coy-coburn/Team24/Old Project/Modified White Paper.pptx

Smart Sprinkler System Project Goal: The goal of this project is to create a system where a person’s lawn is routinely probed and cared for by an automatic sprinkler system. Deliverables Fall 2015: Robot w/ probe, weather monitoring via internet, w/ interface app Spring 2016: Robot charging station, Robot collision-avoiding sensors, pathing memory within box, controller connected to sprinkler system

Team 24: Coy Coburn, Daniel Miller, Michael Turner, Tyler Castro

Robot maneuvering

Power

Controller

Mobile app

Robot sensors

Moisture measurement

Weather data mining

## Slide 2

Subsystem | Primarily Responsible Team Member | Student Responsibilities/ Tasks
Power | Daniel | Prepare the necessary power supply for both the probe as well as the sprinkler system.
Controller | Coy | Create a connection between the master controller with its slave connections; these include the probe, the sprinkler system, and the interface app.
Robot maneuvering | Daniel | Enhance the robot’s ability to maneuver off-terrain and possess the ability to set a route for probing locations.
Robot sensoring | Michael | The robot will need the functions to sense its surroundings and take necessary precautions to avoid obstacles and safely maneuver a lawn.
Moisture measurement | Tyler | IR sensors will be set to sample water moisture in multiple locations in the lawn and reset said probe.
Mobile App | Coy | A mobile app will be created for a user to view sprinkler settings as well as make changes to planned watering for the week or its default.
Weather Data Mining | Michael | The sprinkler master controller will need to connect to weather websites via internet so to plan watering settings for the upcoming week.

## Slide 3

INTERNET

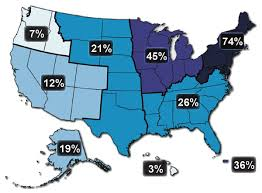
[picture p73: figure]

PRECIPITATION DATA

Control Box
Will handle all the data analysis and communication. Will also charge the robot.

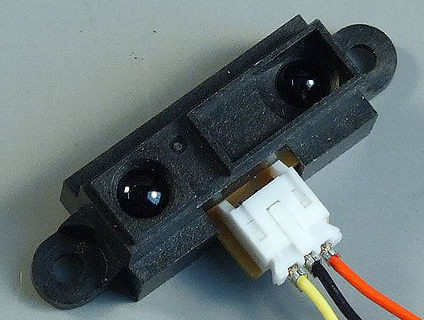
[picture p74: figure]

IR DATA

DATA RESULTS

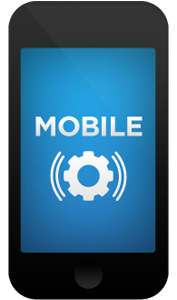
[picture p75: figure]
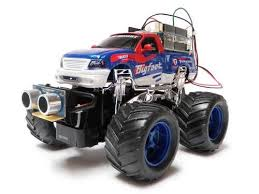
[picture p76: figure]

LOCATION DATA

POWER

USER FEEDBACK

## POWER

- Functional requirements-Provide power for the control station, provide charging capability for the robot
- Design parameters- Central control must be able to provide correct power requirements for the main controller and robot charge station.
- Primary constraints- Step down from 120V AC to microcontroller voltage and battery charging voltage
- Limiting factors-cost, size, Portability

## POWER

| Cost of power (Least important) | Size | Portability (most important)
Battery | High,frequent changing of batteries | Medium, depends on battery type | High
Wall outlet | Low | Medium | Low, needs cord
Custom (outlet/battery combination) | Medium | Medium, depends on battery type | Medium, outlet for controller but batteries for robot

## POWER

We selected the combination of batteries for the robot and direct connection to a wall outlet for the station housing a charging station and the microcontroller for the entire system. The station would consume too much power to rely on batteries, and the cost would become too high. In order to keep the robot mobile, we have decided to give it batteries while allowing it to charge while not in use in the station.

## CONTROLLER

- Functional requirements-can send and receive data from the robot and the mobile device. Will also analyze data taken from the robot and the internet. Control the sprinklers
- Design parameters-it will need reliable wifi connection with internet and robot. The system will need adequate memory to store and calculate data. GPIO pins are needed for sensor connections.
- Primary constraints- TCP function is preferred, a RAM of at least 256 mB and max of 1kB flash is needed. At least 10 pins will be needed
- Limiting factors-cost, processing time, memory size, Wi-Fi/bluetooth, external interfacing options, and ease of programing

## CONTROLLER

| cost (most Important) | processing time | memory size | Wi-Fi (least Important) | external interfacing options
Raspberry Pi B+ | $29.95 | 700 MHz (SoC) | 512 mB (RAM) | Ethernet port, can use wifi adapter | 26 GPIO
RCM5400W | $119 | 74 MHz (microprocessor) | 512 mB (RAM) | Integrated | 39 GPIO, startup,status, reset in/out
BeagleBone Black | $55 | 1 GHz (SoC) | 512 mB (SDRAM) | Ethernet port, can use wifi adapter | 46 GPIO
TI Tiva | $20 | 140 MHz | 256 mB (SRAM) | Ethernet port, can use wifi adapter | 40 GPIO

## CONTROLLER

While most, if not all, of the choices would probably work for our controller, the TI Tiva board was chosen for its relatively cheap price and met all of the required constraints. While the Raspberyy Pi B+ and Beaglebone Black were also decent choices, the are System on Chips, which is much more than we actually need.

## ROBOT MANEUVERING

- Functional requirements-navigate multiple terrains and location knowledge. It will also need wifi capability with the controller.
- Design parameters- the motors must not deplete the battery before it has completed its circuit. Motors must also possess enough torque to move the robot.
- Primary constraints- less than 10 A on battery draw, enough torque to easily move at most 2.5 kg load.
- Limiting factors- torque, power usage, and cost

## ROBOT MANEUVERING

| Torque (kg-cm) (40%) | Power usage (30%) | Cost (30%)
HS-422 Servo Motor | 4.1 | .9 (No-load) at 6.0 V | $9.69 * 2
DC Toy / Hobby Motor | .02 | .42 W (No-load) 1.5 W (loaded) at 6.0 V | $1.95 * 2
2WD microcontoller platform | 1.92 | .426 W (No load) 2.82 W (loaded at 6.0 V | $22.49
B0081C5B80 | .08 | 1.5 W (loaded) at 6.0 V | $6.40 * 2

## ROBOT MANEUVERING

The 2WD microcontoller platform has a relatively nice balance of torque and power consumption, but is the highest in cost. The HS-422 Servo Motor has the highest power consumption, but the highest torque. High torque is necessary for allowing our robot to traverse through grass easier, so the HS-422 Servo Motor is the motor we have decided on.

## ROBOT SENSORS

- Functional requirements- object avoidance, Bluetooth capability with the controller box.
- Design parameters- Distance at which installed sensor discovers an obstruction, time taken to correct pathing
- Primary constraints- Correction time must be quick enough to keep from colliding with obstruction, to preferably keep the robot continuously running
- Limiting factors- cost, sensor accuracy, reaction time, and distance

## ROBOT SENSORS

| Cost (60%) | Distance (40%) | Overall (of 10)
PING))) Ultrasonic Distance Sensor | 5 | 2 | 3.8
PmodMAXSONAR - Ultrasonic Range Finder | 4 | 10 | 6.4
Devantech SRF05 Ultrasonic Range Finder | 6 | 2 | 4.4
Sharp GP2Y0A21YK0F Analog Distance Sensor 10-80cm (https://www.pololu.com/product/136/specs) | 8 | 6 | 7.2

## ROBOT SENSORS

Although the PmodMAXSONAR - Ultrasonic Range Finder is very effective and has a massive range, the tradeoff for its cost of $30 doesn’t stand up to the overall quality of the Sharp GP2Y0A21YK0F Analog Distance Sensor 10-80cm (https://www.pololu.com/product/136/specs). The range of the PmodMAXSONAR is unnecessary, with it’s maximum range of 645 cm, and the range of the Sharp Sensor is satisfactory while at a third of the price.

## MOISTURE MEASUREMENT

- Functional requirements-moisture detection, data transmission
- Design parameters- Current readings from the two photodetectors, voltage difference of the two voltages after passing through the transimpedance amplifier, output of the comparator
- Primary constraints- For the diodes, forward voltage must not exceed 1.55 V, and reverse voltage must not exceed 5 V.
- Limiting factors- accuracy, cost, quality

## MOISTURE MEASUREMENT

| Accuracy (50%) | Cost (50%) | Overall (of 10)
THORLABS LED910E NIR LED | 5 | 9 | 7.5
THORLABS LED1050E NIR LED | 7 | 5 | 6
THORLABS LED1550E NIR LED | 8 | 3 | 5.5
THORLABS FGA01 Photodetector | 8 | 1 | 4.5
DigiKey 751-1006-ND Photodetector | 5 | 10 | 7.5

## MOISTURE MEASUREMENT

In order to get the highest amount of accuracy from the photodetector/NIR LED combination, we would want the highest difference in wavelength between the two LEDs, as that would create the largest difference in absorption from water, allowing for greater precision in voltage difference. However, price becomes an issue when purchasing higher wavelength LEDs. Although the price of the 1050 and 1550 nanometer LEDs is the same from THORLABS, the price of a photodetector in the spectral range for 1550 nanometers skyrockets to ~$50 for the THORLABS FGA01, compared to DigiKey’s 751-1006-ND, which is priced at around $1. Therefore, the sufficient tradeoff would be to use the 910 and 1050 nanometer LEDs paired with two 751-1006-ND photodetectors, which both fall within the spectral range, while keeping price to a minimum.

## MOBILE APP

- Functional requirements-real-time notification of sprinkler settings to user, user ability to modify sprinkler settings.
- Design parameters-an eye-pleasing GUI is preferred for use, simple buttons and toggles for user interaction is required.
- Primary constraints- operate available memory given through mobile app
- Limiting factors- GUI, ease of use, and development time

## MOBILE APP

| GUI (least important) | Ease of use (most important) | Development time
Android | Free GUI Android set | Open-source | Simple
IOS | iPhone GUI PSD | Closed-source | Complex
Windows | NET/XAML, Win32 | Closed-source (technically) | Medium

## MOBILE APP

The team has chosen to use Android app development system. While not only is Android an open-source model, recent news has shown that Android apps will also be usable on Windows phones, increasing the amount of potential users. It is also a pro that Android development is a common beginning for many application programmers. This can be seen with the amount of help and tutorials on designing mobile Android app interfaces and functions.

## WEATHER MINING DATA

- Functional requirements- ability to connect to interweb and retrieve weather data
- Design parameters- choosing language that allows for most firmware/internet interaction via sockets, and the choice of weather websites
- Primary constraints- accuracy of website, versatility
- Limiting factors- runtime, complexity, and design

## WEATHER MINING DATA

| Runtime (Most Important) | Complexity (Least Important) | Design
Java | High | Higher-level | Application oriented
C++ | Low | Low-level | Hardware oriented
Python | Medium | Low-level | Web oriented

## WEATHER MINING DATA

We have chosen to build our program on C++ for its hardware oriented design, which will prove useful when interfacing with the board. While not as easy to manipulate the internet compared to web-oriented Python, it still has complete functionality with usage of sockets.

## Slide 25

Subsystem | Subsystem Tasks | Subsystem Specs
Power | Provide power to the robot and controller | Step down from 120V AC to voltage requirements for robot and controller.
Controller | Receive and interpret data sent by the robot | A reliable wifi connection is needed, and TCP packaging is preferred for data transfer.
Controller | Receive and interpret information from internet | A reliable wifi connection is needed, and TCP packaging is preferred for data transfer.
Controller | Calculations made to create sprinkler settings for upcoming week | 256 Mb to calculate sprinkler settings rom received data, and 1 Mb flash to store settings made from calculations.
Robot maneuvering | Allow robot to move efficiently through grassy terrain | Motors need enough torque move and turn robot of at least 2.5 kg. Also possibly 4 motor-powered wheels for slopes and muddy terrain.

## Slide 26

Subsystem | Subsystem Tasks | Subsystem Specs
Robot sensors | Measure distance of foreign objects in front of robot | Measurable distance of at least 50 cm in front of robot to allow for turning.
Moisture measurement | Detect moisture in lawn section | Voltage in diode circuit must not exceed its listed voltage maximums in datasheets.
Moisture measurement | Send found data to controller | A reliable wifi connection is needed, and TCP packaging is preferred for data transfer.
Interface app | Keeps user up to date on expected sprinkling | Needs to be simple and user-friendly, sends at least 3 notifications a week
Interface app | Give user ability to influence sprinkler settings | App should have tabs/toggles for time/day of watering, time amount for watering, sections to water, and setting to turn on/off sprinkler system.
Weather Mining Data | Connects app to weather data online, feeds info to app and controller box | Needs to have reliable connection
