coy-coburn/Team24/Old Project/pro-con sensor net v robot.docx

Sensor net

- pro
  - easier to build
- con
  - harder to put in place
  - hard to repair
  - power over long distance is expensive

robot

- pro
  - easy to use
  - easy to repair
- con
  - more room for error
