coy-coburn/Team24/photos/Atenna.JPG

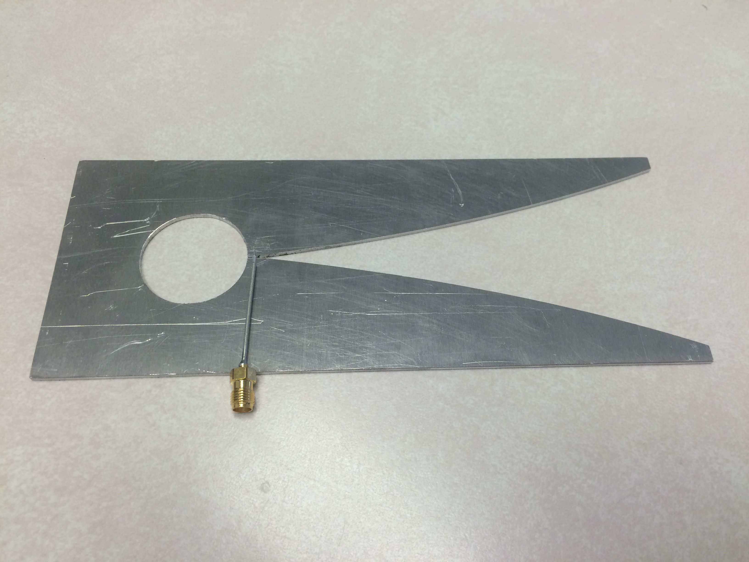
photos/Atenna.JPG
