coy-coburn/Team24/photos/LNA.JPG

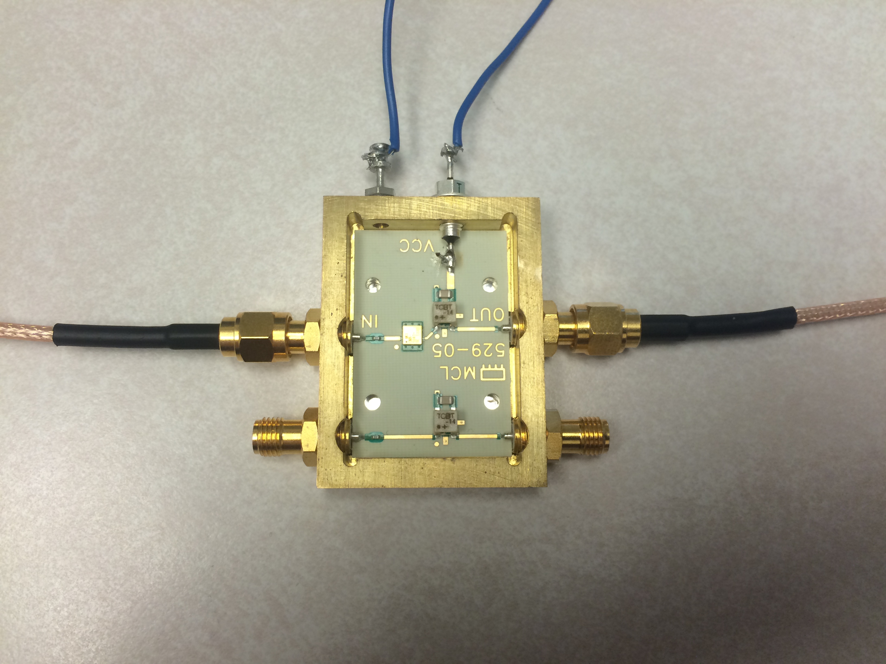
photos/LNA.JPG
