coy-coburn/Team24/photos/lnablock.jpg

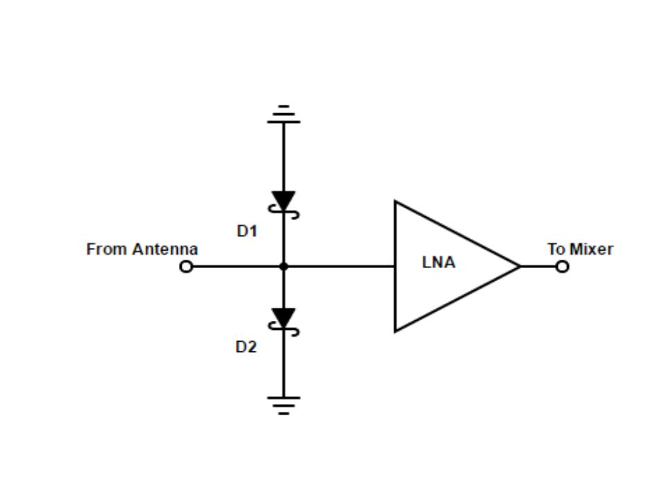
photos/lnablock.jpg
