coy-coburn/Team24/photos/Mixer.jpg

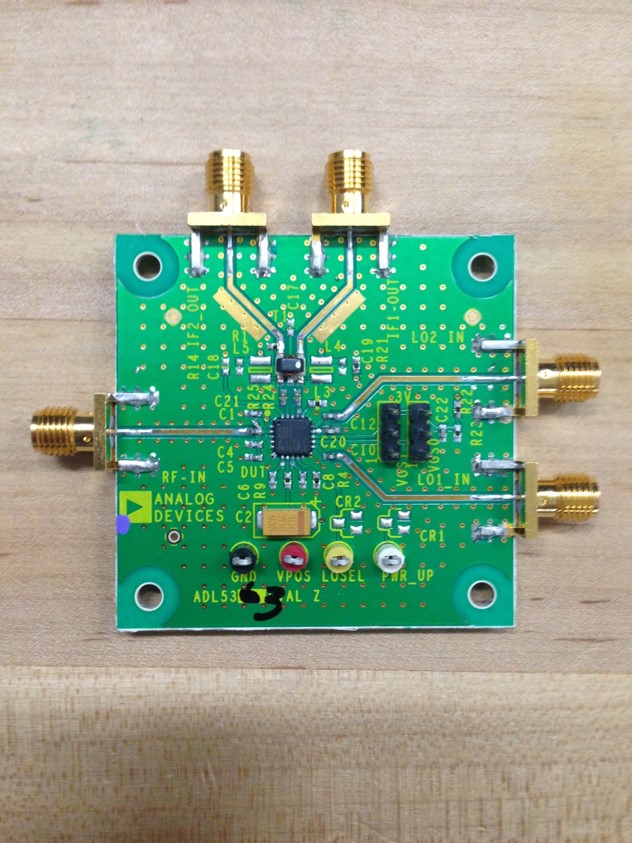
photos/Mixer.jpg
