coy-coburn/Team24/photos/Reciver Conversion Subsystem.jpg

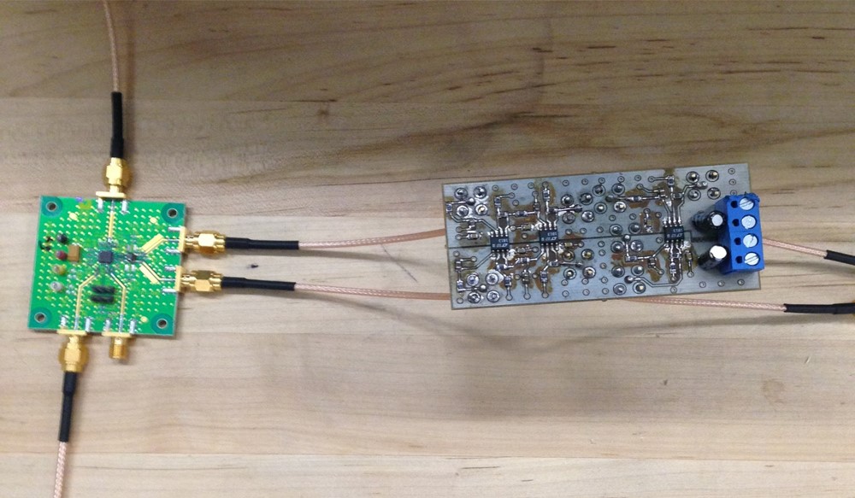
photos/Reciver Conversion Subsystem.jpg
