coy-coburn/Team24/photos/Reciver Cuircut Subsystem.JPG

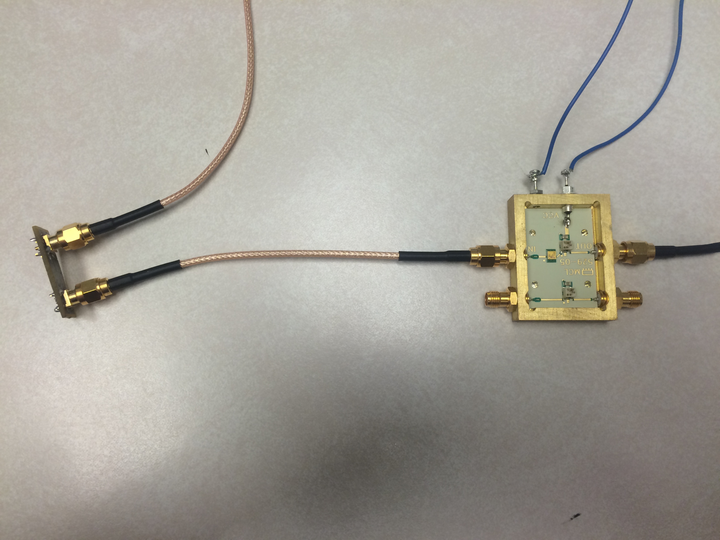
photos/Reciver Cuircut Subsystem.JPG
