coy-coburn/Team24/photos/SystemPic.PNG

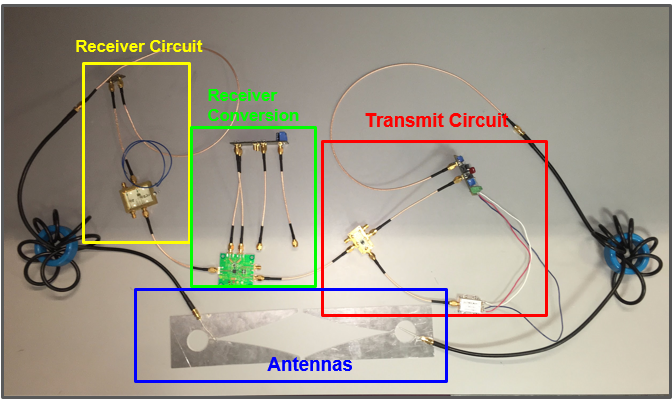
photos/SystemPic.PNG
