coy-coburn/Team24/photos/Transmiter.png

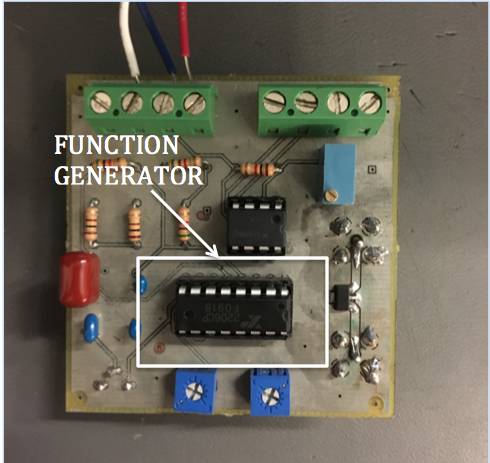
photos/Transmiter.png
