coy-coburn/Team24/photos/VCO.jpg

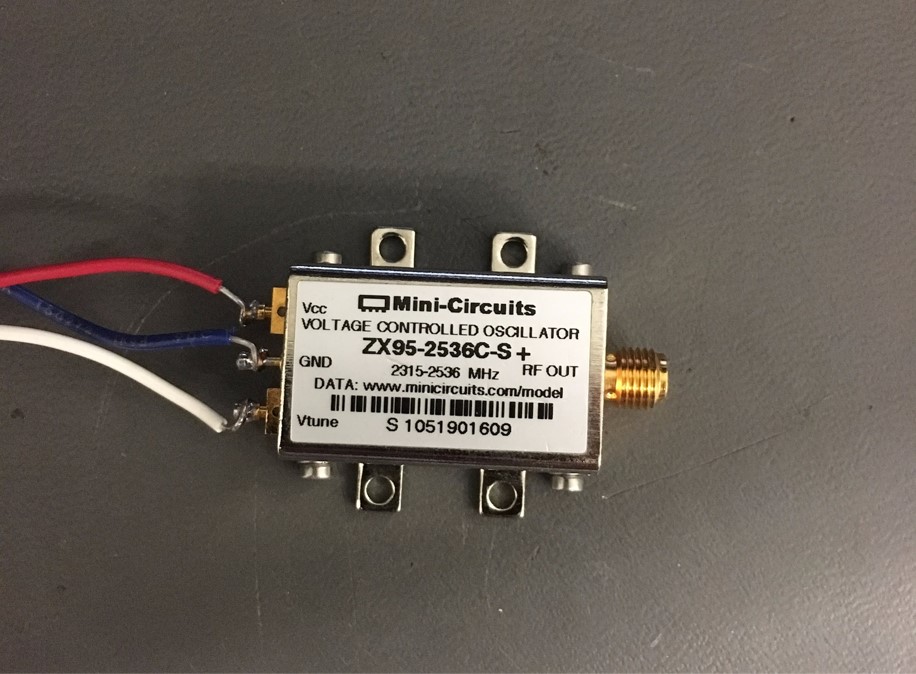
photos/VCO.jpg
